VioletDev0608/Yari/images/image6.png

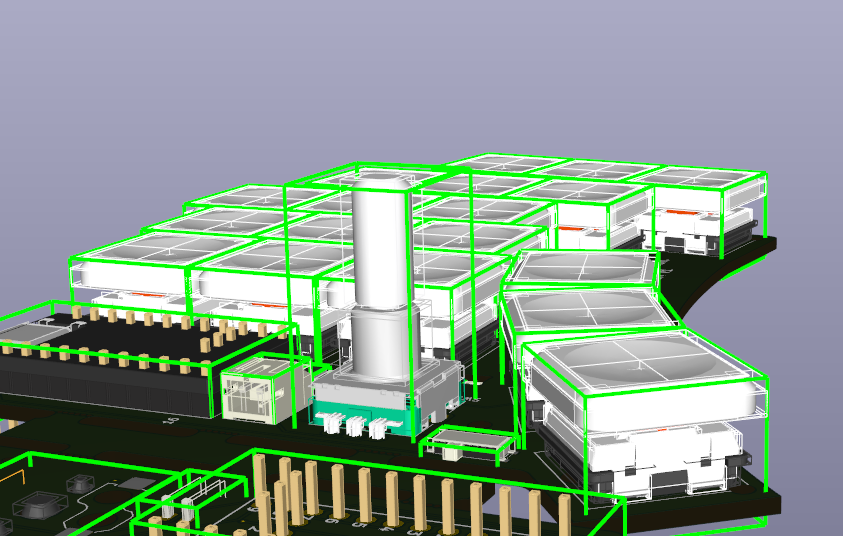
images/image6.png
