VioletDev0608/Yari/images/image1.png

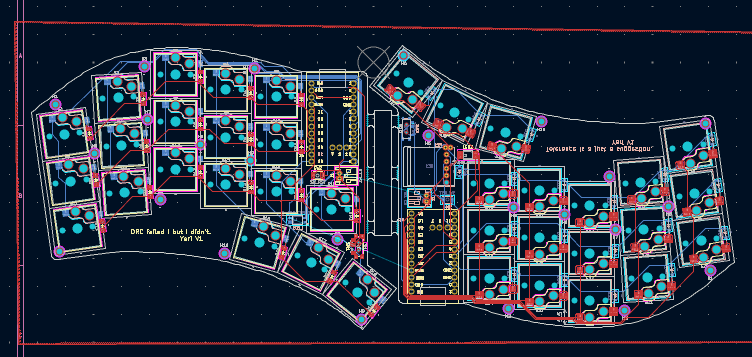
images/image1.png
