VioletDev0608/Yari/images/image2.png

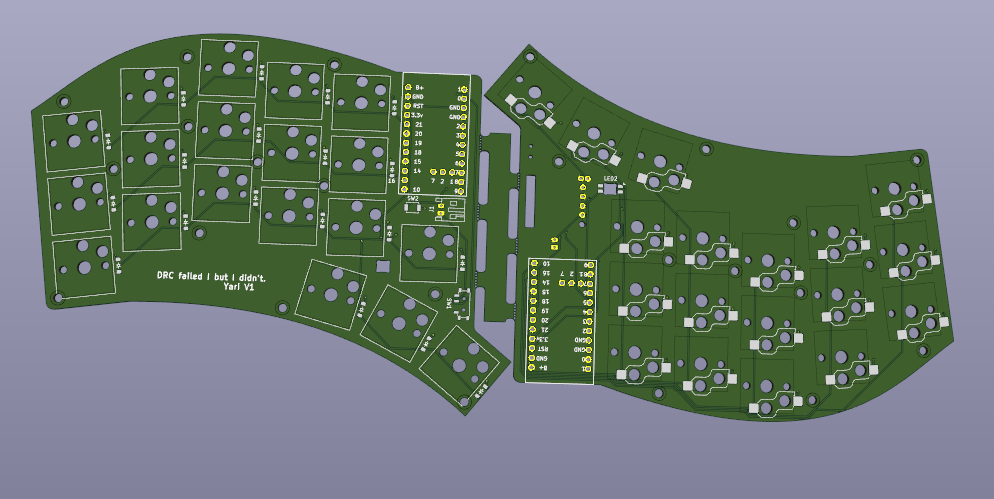
images/image2.png
