VioletDev0608/Yari/images/image3.png

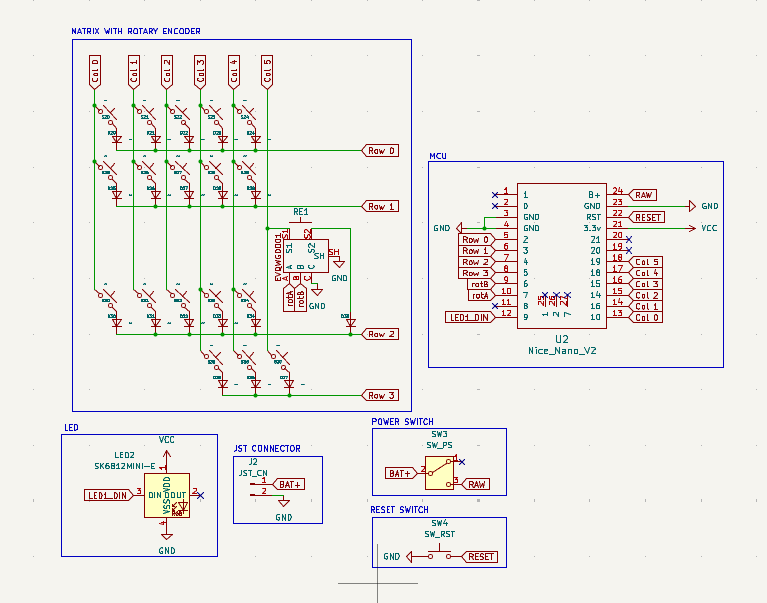
images/image3.png
