VioletDev0608/Yari/images/image4.png

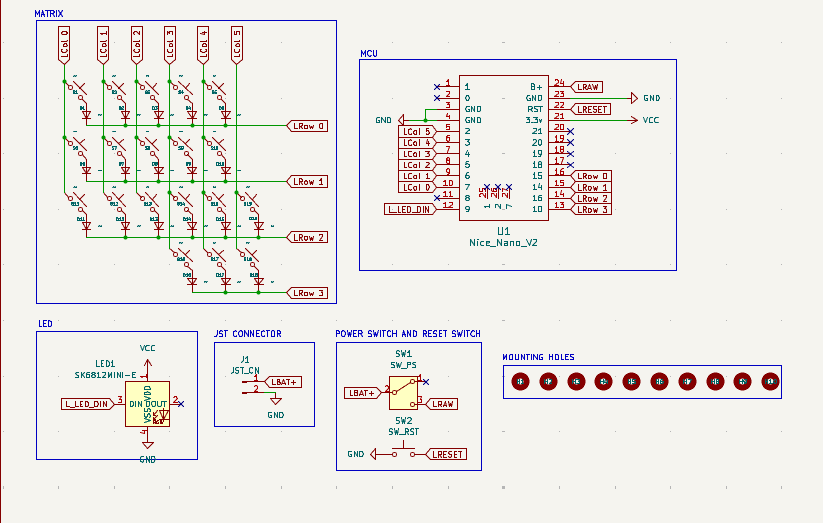
images/image4.png
