VioletDev0608/Yari/images/image5.png

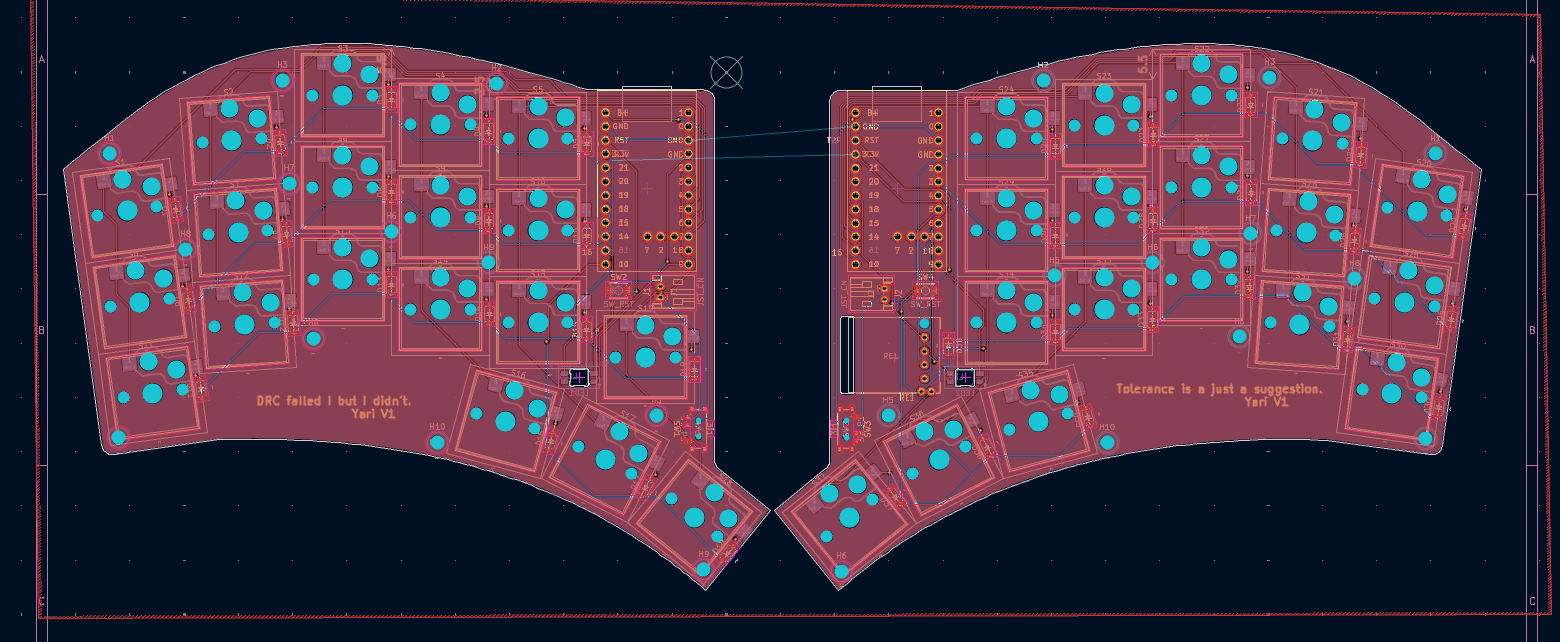
images/image5.png
