VioletDev0608/Yari/images/image8.png

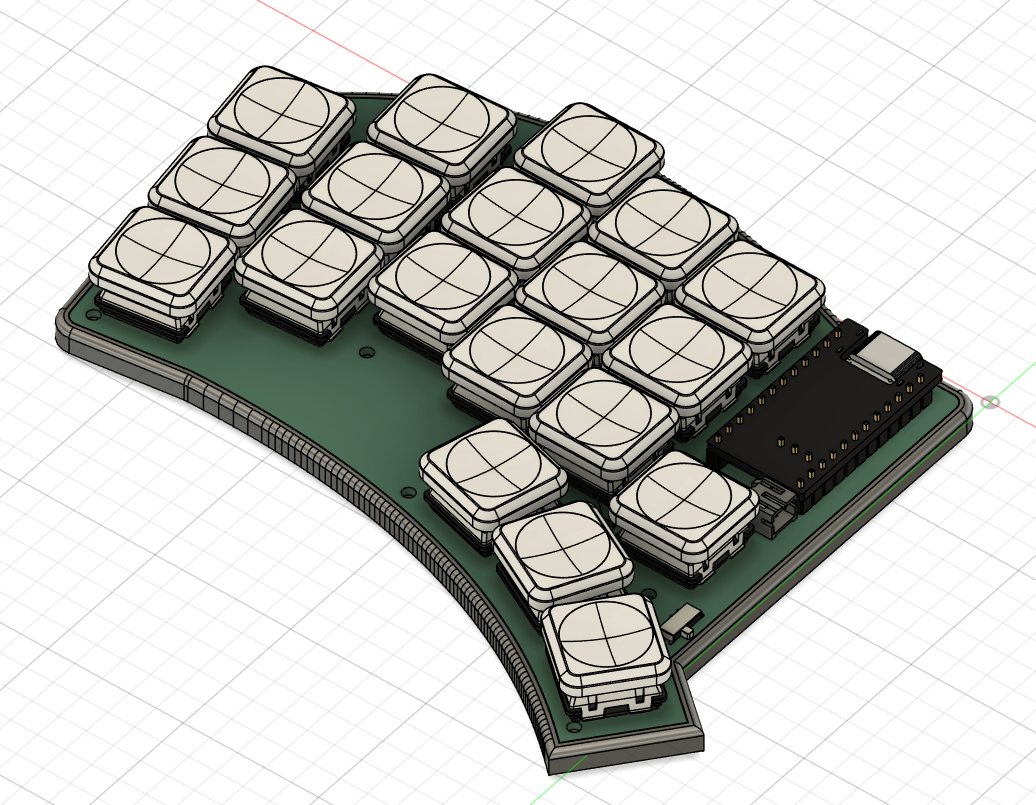
images/image8.png
