VioletDev0608/Yari/images/image9.png

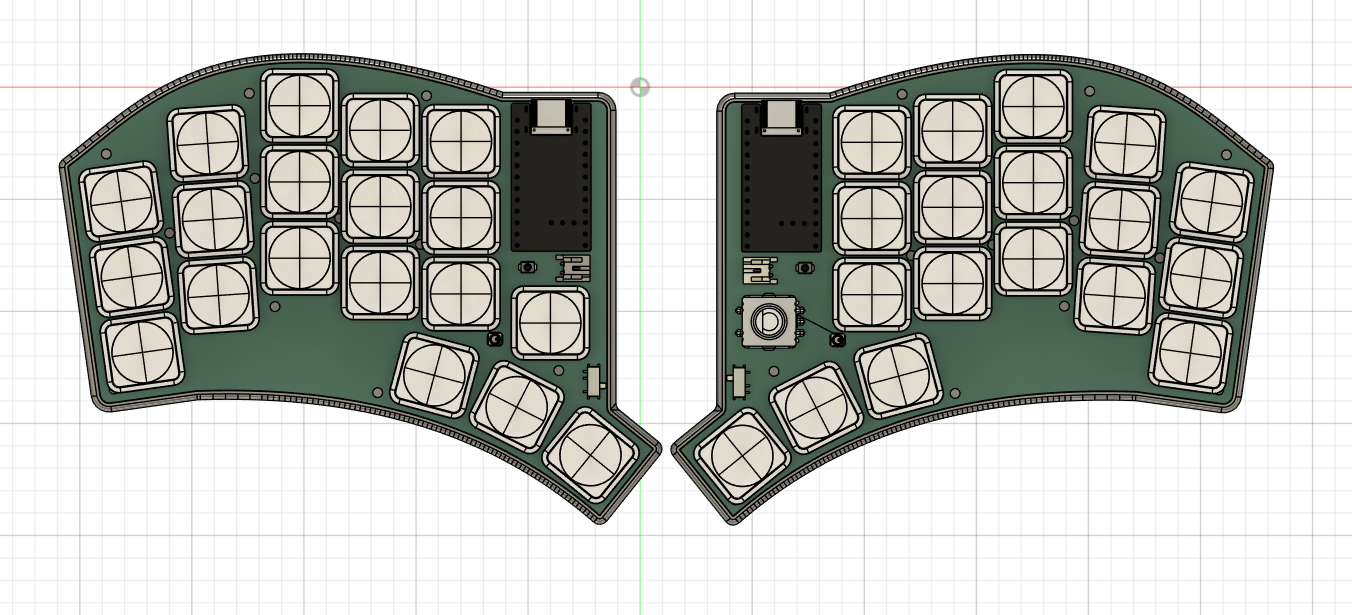
images/image9.png
