VioletDev0608/Yari/images/image10.png

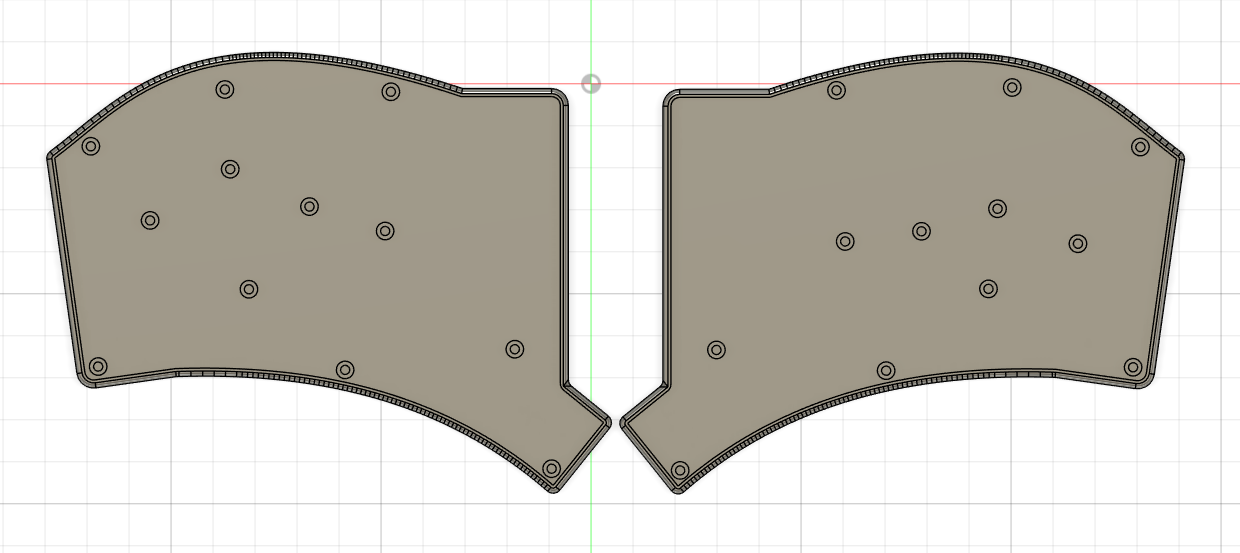
images/image10.png
