VioletDev0608/Yari/images/image11.png

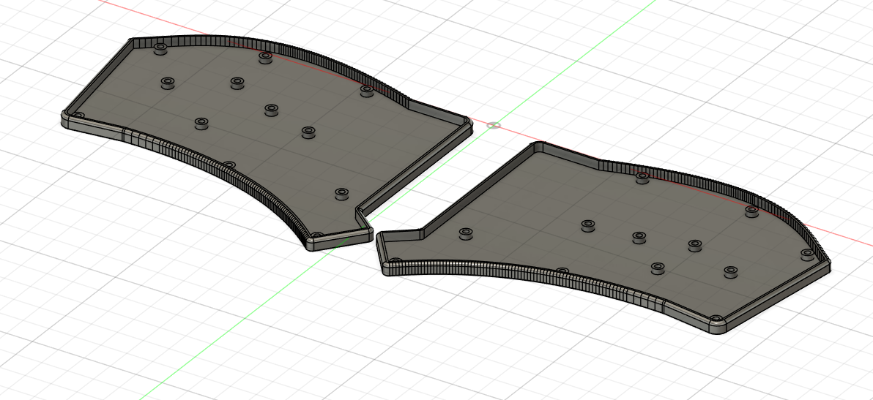
images/image11.png
