VioletDev0608/Yari/images/image12.png

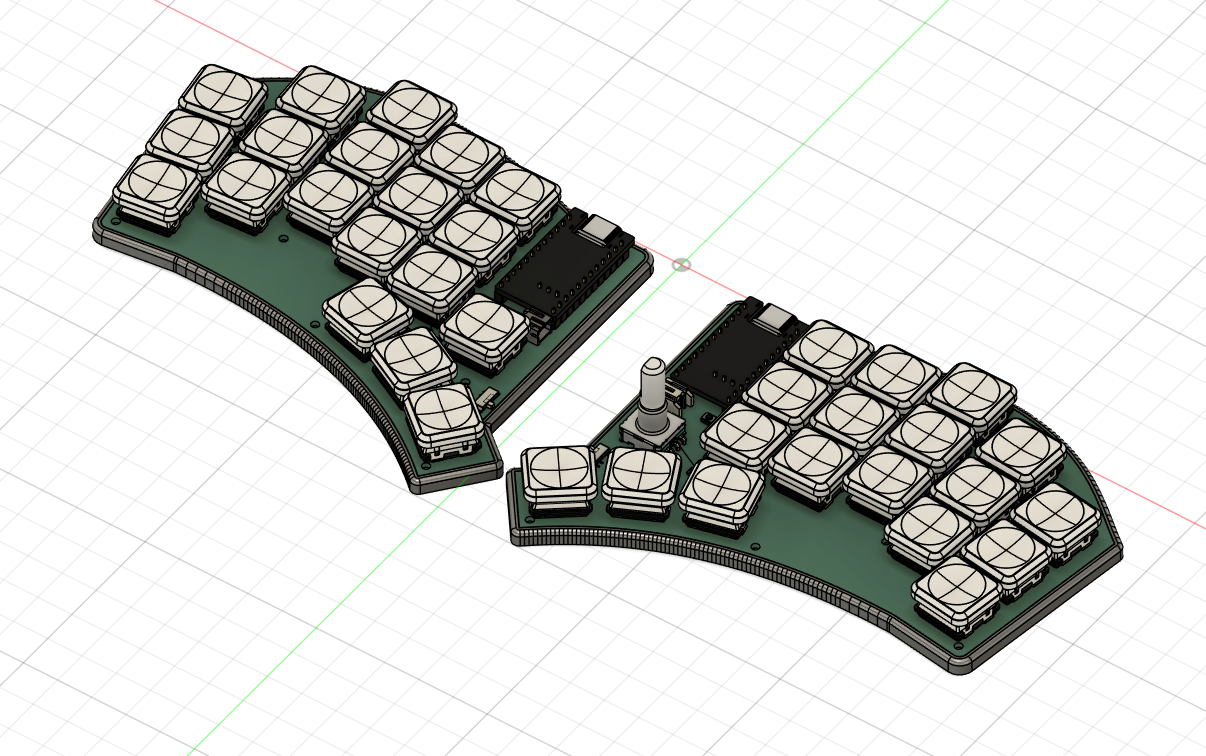
images/image12.png
