VioletDev0608/Yari/images/image13.png

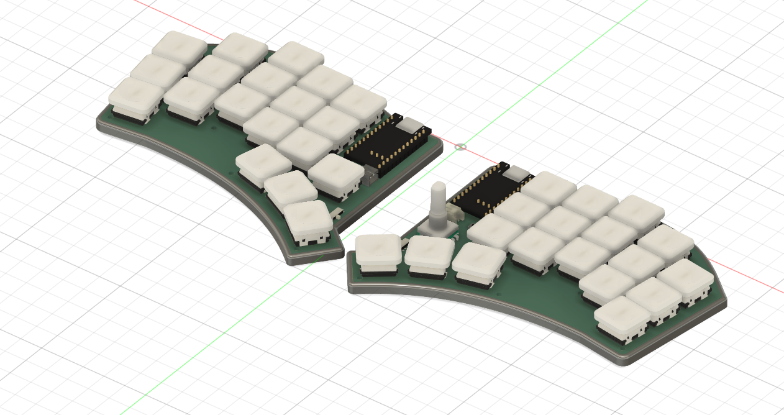
images/image13.png
