VioletDev0608/Yari/images/image14.png

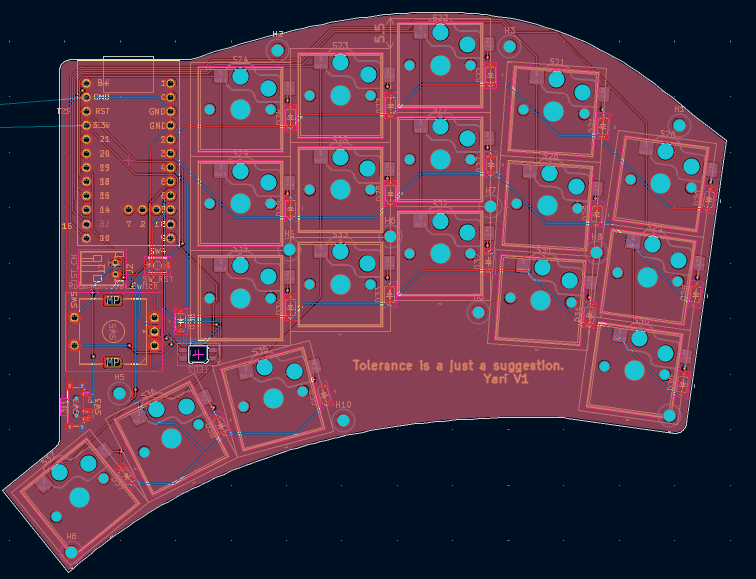
images/image14.png
