VioletDev0608/Yari/images/image15.png

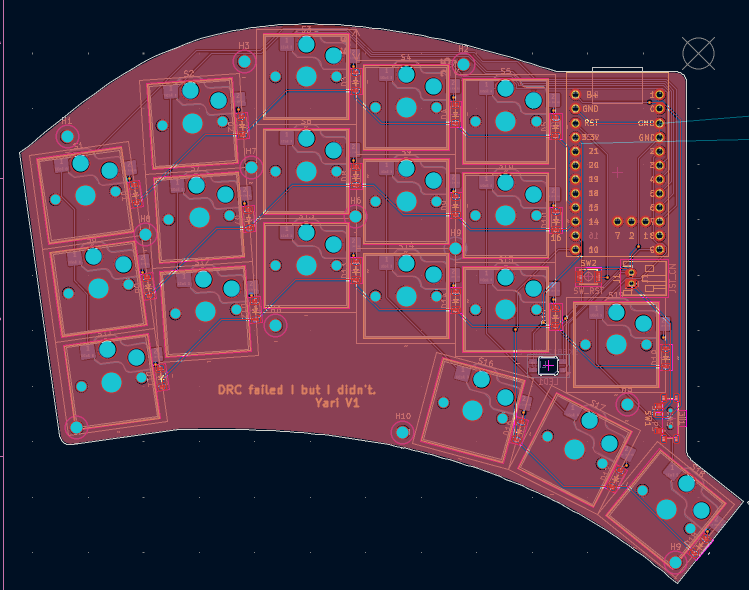
images/image15.png
