VioletDev0608/Yari/images/image16.png

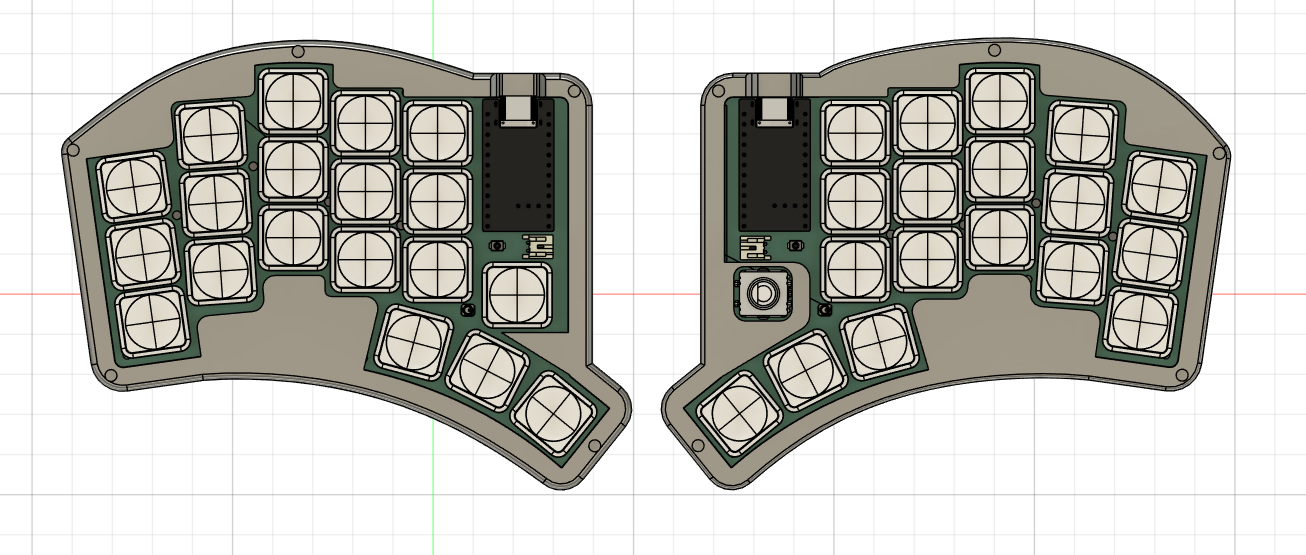
images/image16.png
